heyitsmeyo/Smartglove/Random Forest on esp32/classifier.h

#pragma once
#include <cstdarg>
namespace Eloquent {
    namespace ML {
        namespace Port {
            class RandomForest {
                public:
                    /**
                    * Predict class for features vector
                    */
                    int predict(float *x) {
                        uint8_t votes[5] = { 0 };
                        // tree #1
                        if (x[3] <= -0.22238226979970932) {
                            if (x[0] <= 0.14451148733496666) {
                                votes[2] += 1;
                            }

                            else {
                                votes[4] += 1;
                            }
                        }

                        else {
                            if (x[2] <= 1.122367024421692) {
                                votes[1] += 1;
                            }

                            else {
                                votes[3] += 1;
                            }
                        }

                        // tree #2
                        if (x[1] <= 0.183273047208786) {
                            if (x[2] <= -0.9470191895961761) {
                                votes[4] += 1;
                            }

                            else {
                                votes[2] += 1;
                            }
                        }

                        else {
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
                                    votes[3] += 1;
                                }

                                else {
                                    votes[2] += 1;
                                }
                            }

                            else {
                                votes[1] += 1;
                            }
                        }

                        else {
                            if (x[4] <= 0.4811157137155533) {
                                votes[0] += 1;
                            }

                            else {
                                votes[4] += 1;
                            }
                        }

                        // tree #30
                        if (x[0] <= 0.303992822766304) {
                            if (x[9] <= -0.07616996392607689) {
                                votes[3] += 1;
                            }

                            else {
                                if (x[8] <= -0.7067156434059143) {
                                    votes[1] += 1;
                                }

                                else {
                                    votes[1] += 1;
                                }
                            }
                        }

                        else {
                            if (x[8] <= -0.24879039824008942) {
                                votes[4] += 1;
                            }

                            else {
                                votes[0] += 1;
                            }
                        }

                        // return argmax of votes
                        uint8_t classIdx = 0;
                        float maxVotes = votes[0];

                        for (uint8_t i = 1; i < 5; i++) {
                            if (votes[i] > maxVotes) {
                                classIdx = i;
                                maxVotes = votes[i];
                            }
                        }

                        return classIdx;
                    }

                    const char* predictLabel(float *x) {
                        return idxToLabel(predict(x));
                    }
                    const char* idxToLabel(uint8_t classIdx) {
    switch (classIdx) {
        case 0:
            return "A";
        case 1:
            return "B";
        case 2:
            return "J";
        case 3:
            return "W";
        case 4:
            return "Y";
        default:
            return "Unknown"; 
        
    }
}


                protected:
                };
            }
        }
    }
